Bananut-Electronics/MiDispositivoMIDI_V3/images/bananut.png

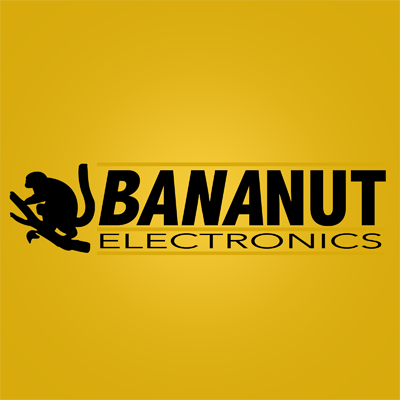
images/bananut.png
