Bananut-Electronics/MiDispositivoMIDI_V3/images/bot.png

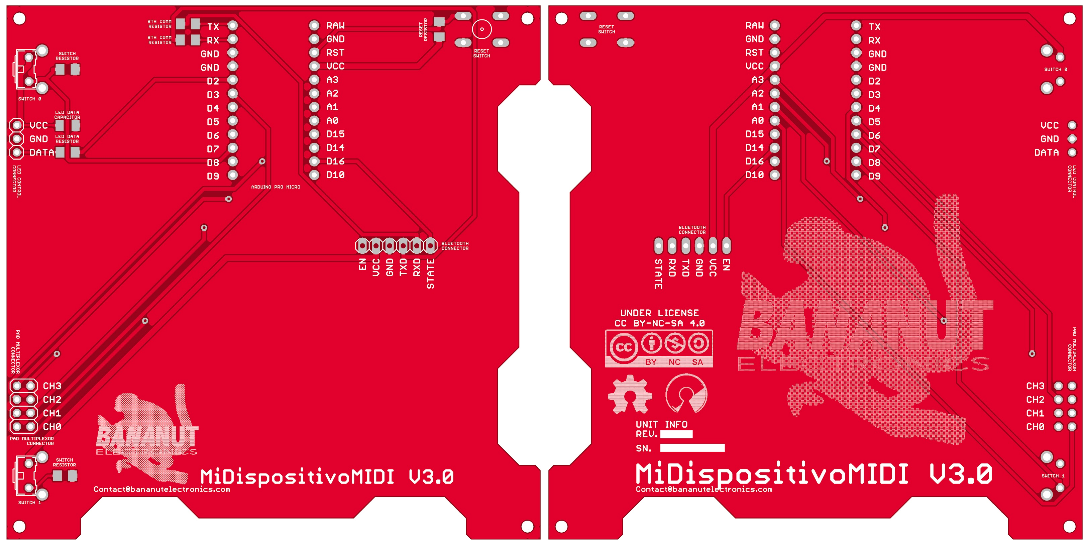
images/bot.png
