Bananut-Electronics/MiDispositivoMIDI_V3/images/front.jpg

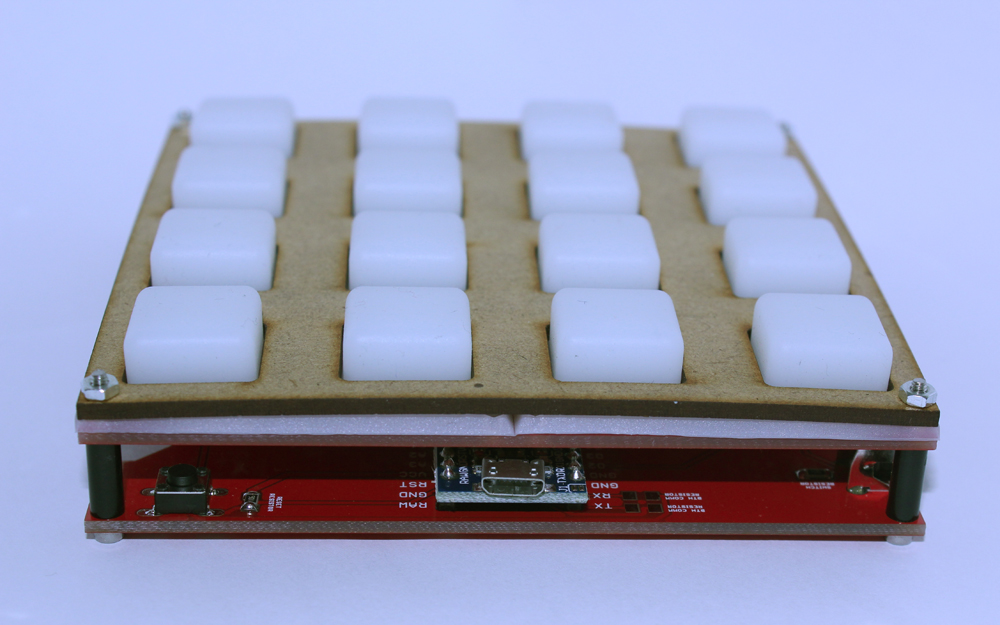
images/front.jpg
