Bananut-Electronics/MiDispositivoMIDI_V3/images/green.jpg

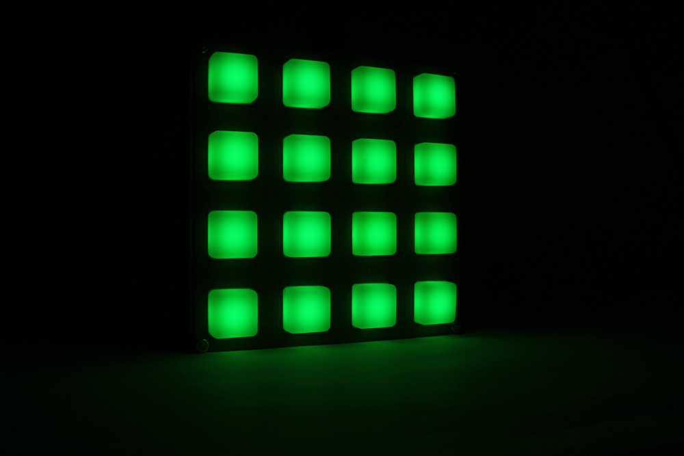
images/green.jpg
