Bananut-Electronics/MiDispositivoMIDI_V3/images/MDM_V3_HW_Arduino.jpg

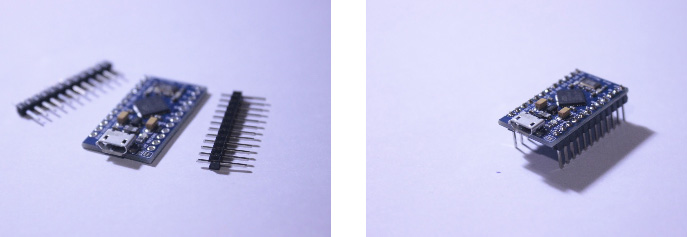
images/MDM_V3_HW_Arduino.jpg
