Bananut-Electronics/MiDispositivoMIDI_V3/images/MDM_V3_HW_ArduinoPinOut.jpg

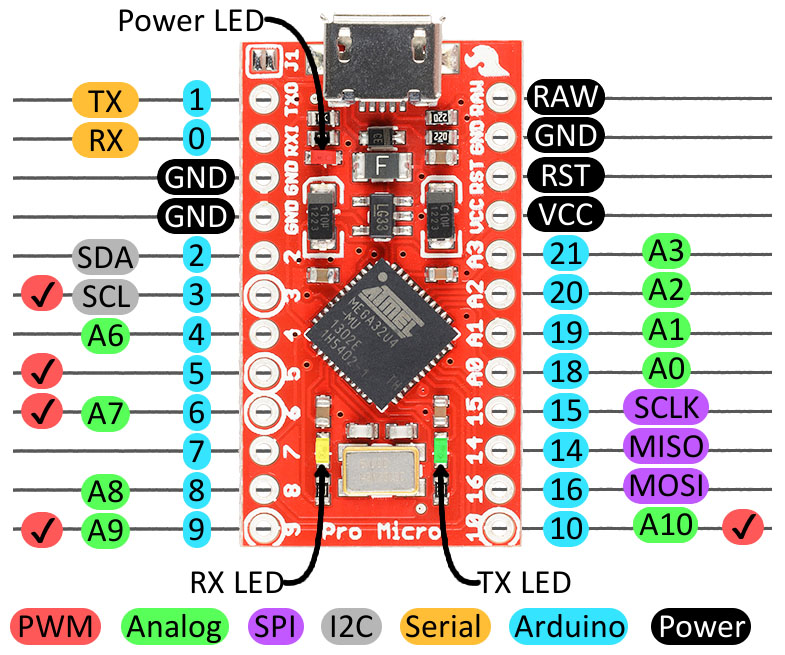
images/MDM_V3_HW_ArduinoPinOut.jpg
