Bananut-Electronics/MiDispositivoMIDI_V3/images/MDM_V3_HW_ControlBoard_PCBCon.JPG

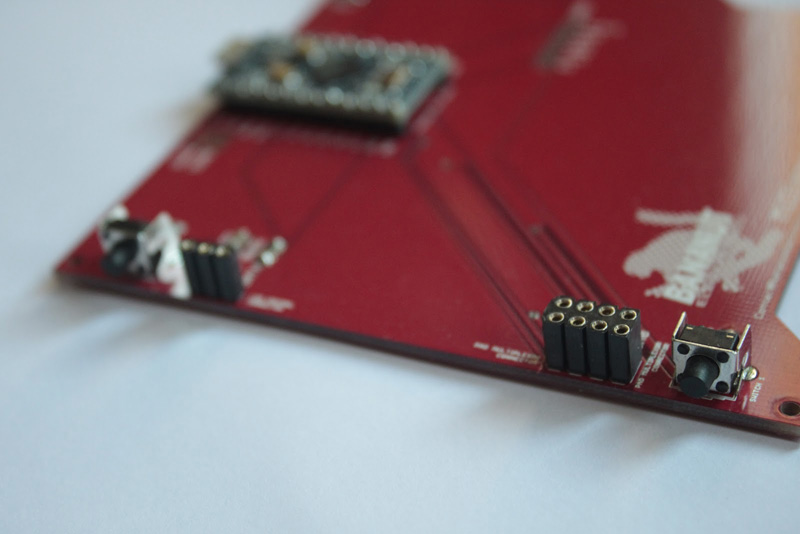
images/MDM_V3_HW_ControlBoard_PCBCon.JPG
