Bananut-Electronics/MiDispositivoMIDI_V3/images/MDM_V3_HW_LEDPad_Connector.JPG

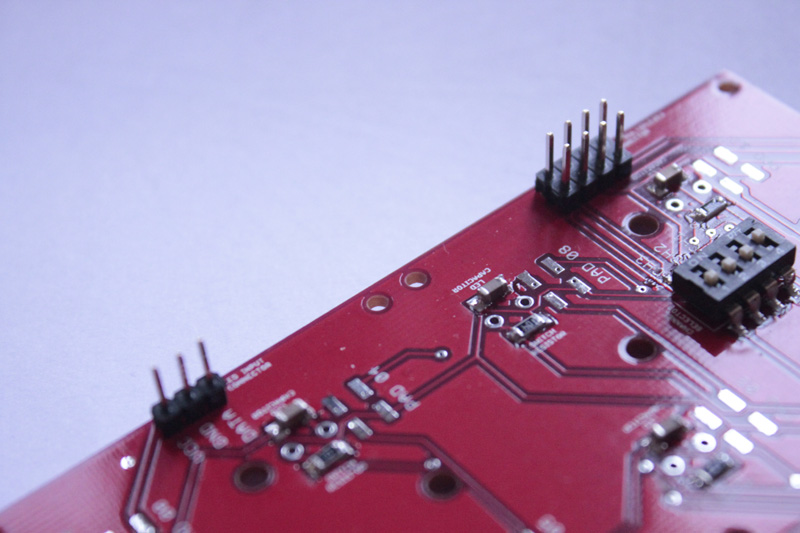
images/MDM_V3_HW_LEDPad_Connector.JPG
