Bananut-Electronics/MiDispositivoMIDI_V3/images/MDM_V3_HW_LEDPad_DIPSW.JPG

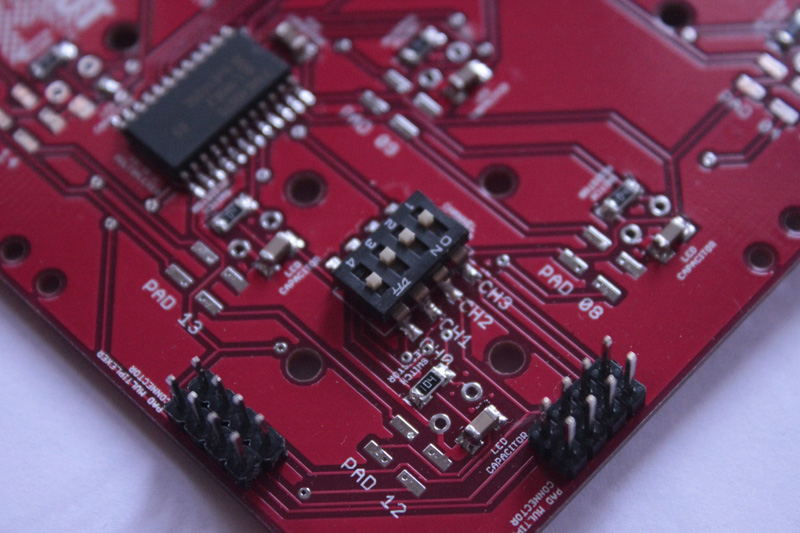
images/MDM_V3_HW_LEDPad_DIPSW.JPG
