Bananut-Electronics/MiDispositivoMIDI_V3/images/MDM_V3_HW_LEDPAD_Layer.jpg

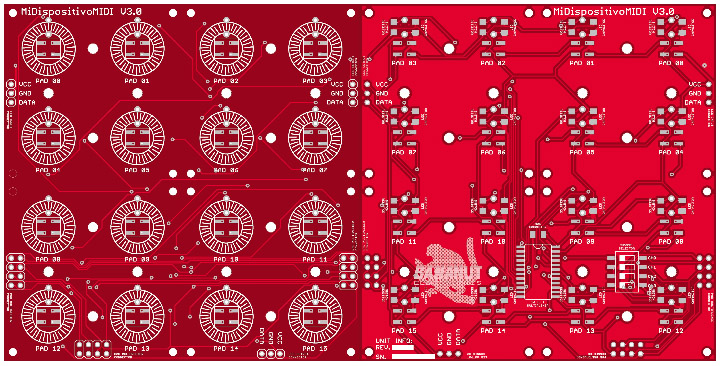
images/MDM_V3_HW_LEDPAD_Layer.jpg
