Bananut-Electronics/MiDispositivoMIDI_V3/images/MDM_V3_HW_LEDPad_SW.JPG

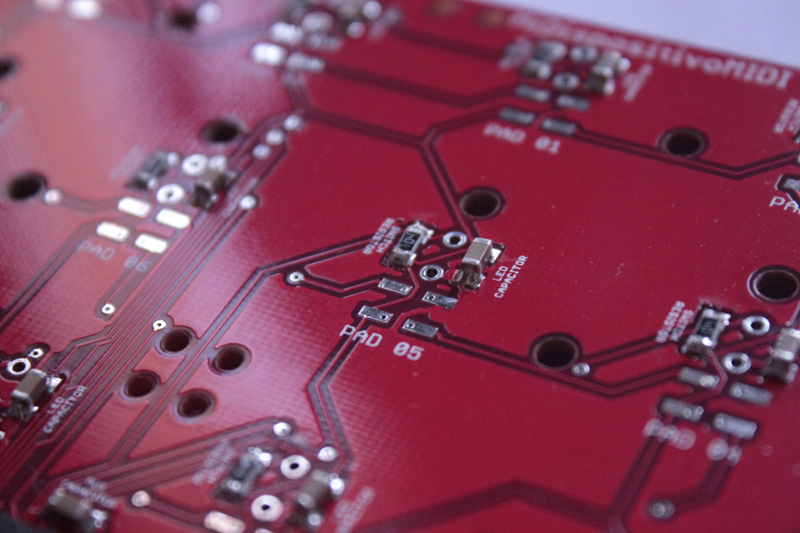
images/MDM_V3_HW_LEDPad_SW.JPG
