Bananut-Electronics/MiDispositivoMIDI_V3/images/MDM_V3_HW_MuxCode.jpg

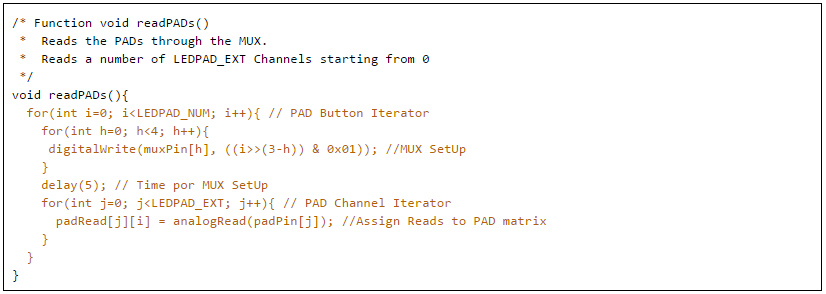
images/MDM_V3_HW_MuxCode.jpg
