Bananut-Electronics/MiDispositivoMIDI_V3/images/MDM_V3_HW_Render.jpg

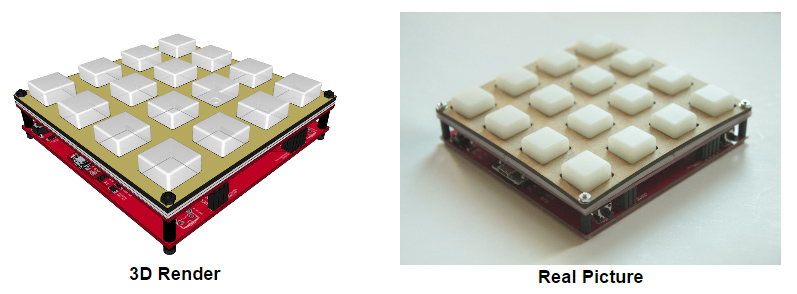
images/MDM_V3_HW_Render.jpg
