Bananut-Electronics/MiDispositivoMIDI_V3/images/MDM_V3_HW_ResetSwitch.JPG

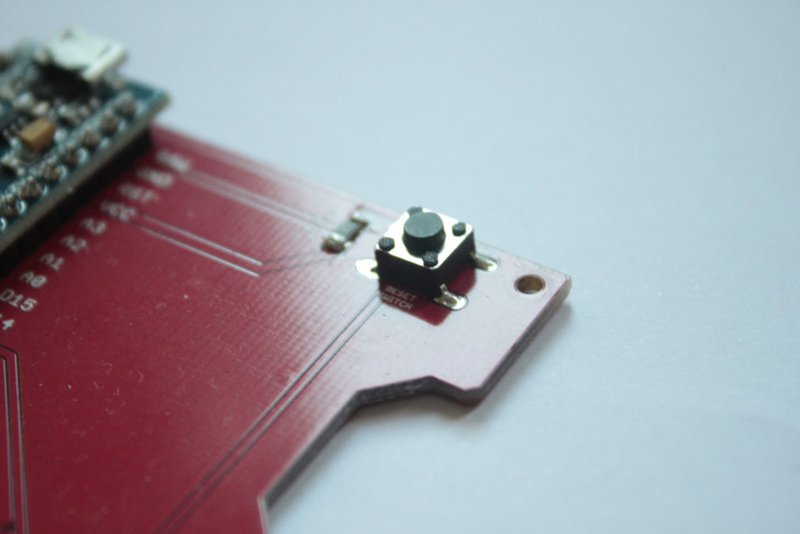
images/MDM_V3_HW_ResetSwitch.JPG
