Bananut-Electronics/MiDispositivoMIDI_V3/images/MDM_V3_HW_SWCircuit.jpg

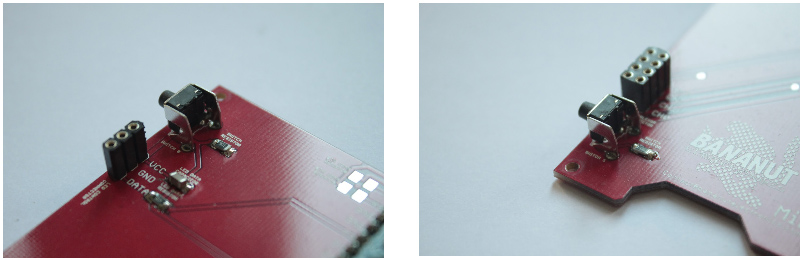
images/MDM_V3_HW_SWCircuit.jpg
