Bananut-Electronics/MiDispositivoMIDI_V3/images/MDM_V3_HW_WS2812B.jpg

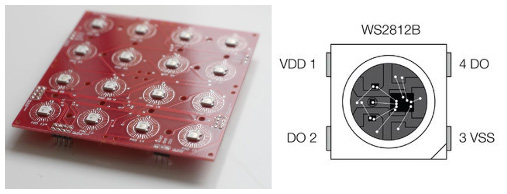
images/MDM_V3_HW_WS2812B.jpg
