Bananut-Electronics/MiDispositivoMIDI_V3/images/MDM_V3_INTRO_Device1.JPG

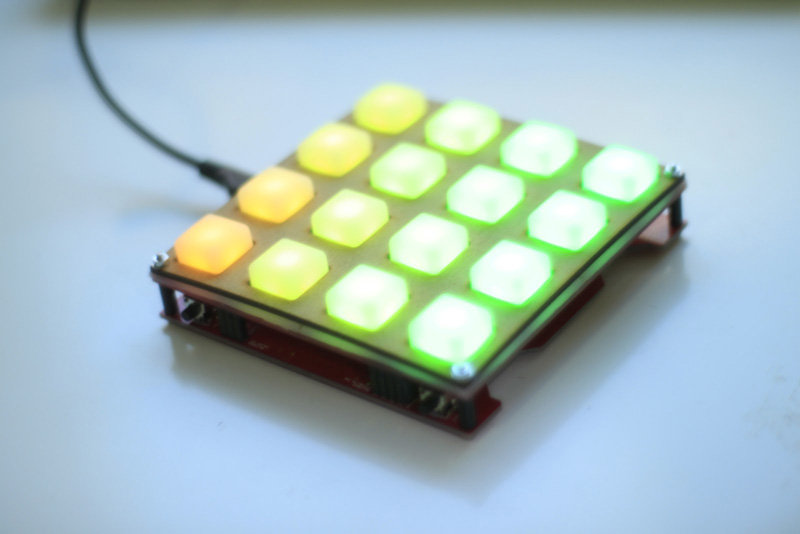
images/MDM_V3_INTRO_Device1.JPG
