Bananut-Electronics/MiDispositivoMIDI_V3/images/top.jpg

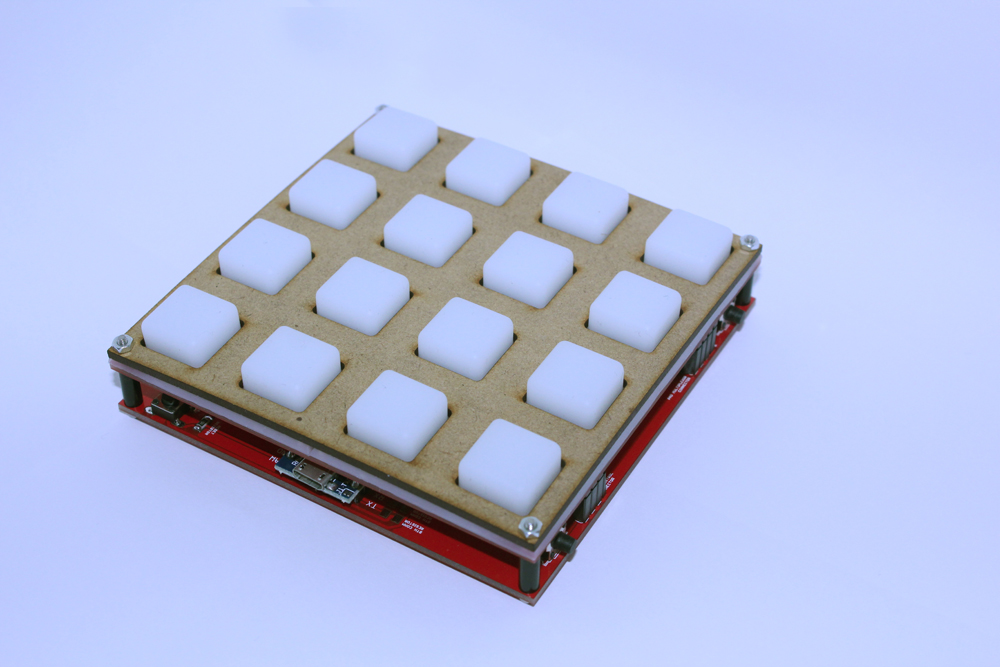
images/top.jpg
