Bananut-Electronics/MiDispositivoMIDI_V3/images/top.png

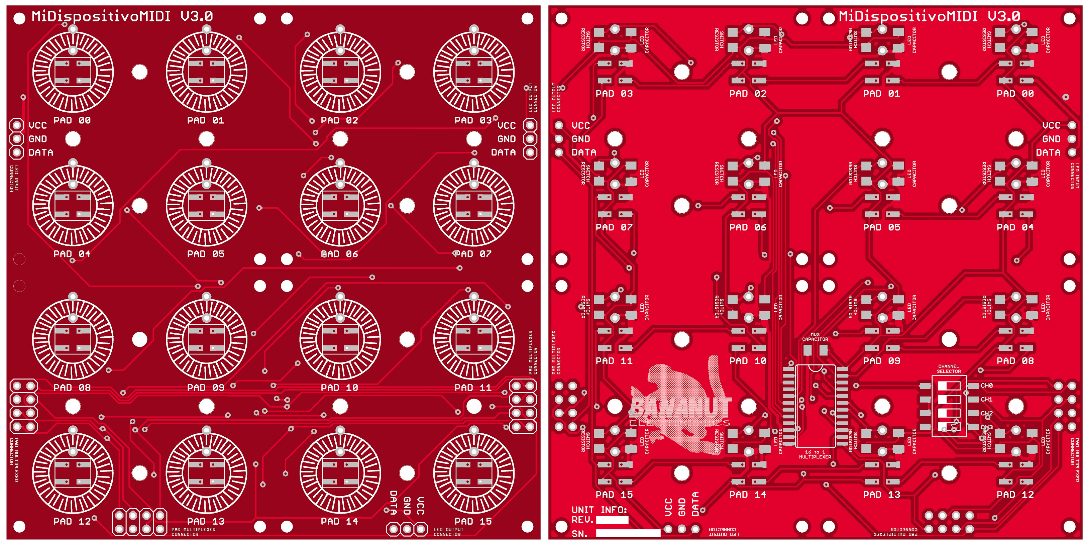
images/top.png
