Bananut-Electronics/MiDispositivoMIDI_V3/images/yellow.jpg

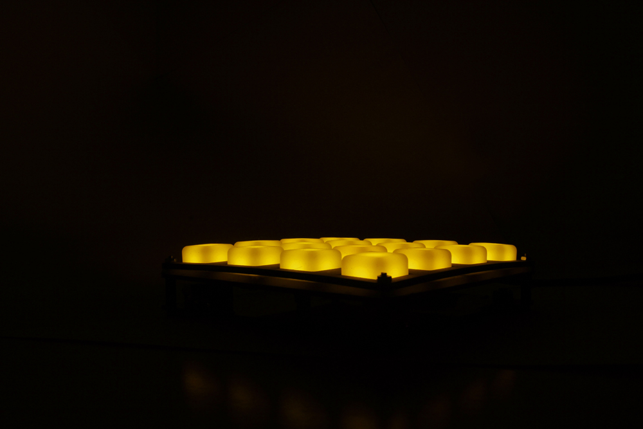
images/yellow.jpg
