Bananut-Electronics/MiDispositivoMIDI_V3/images/MDM_V3_HW_ArduinoSoldered.jpg

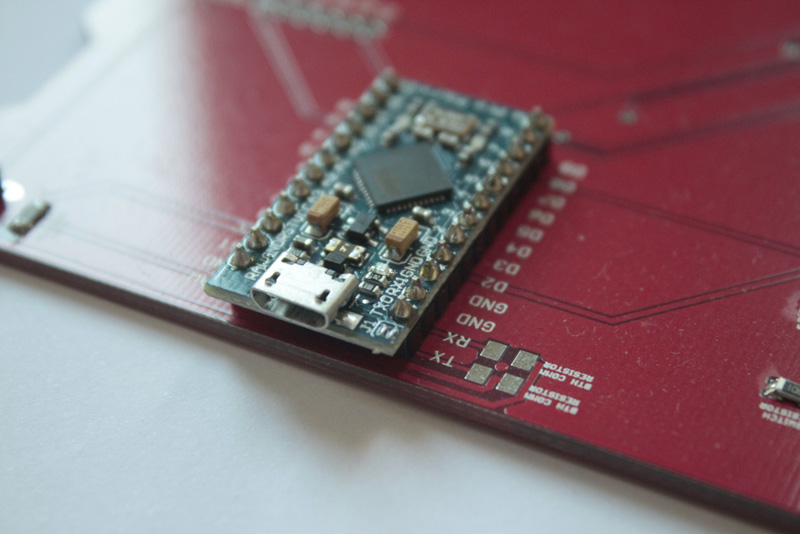
images/MDM_V3_HW_ArduinoSoldered.jpg
