Bananut-Electronics/MiDispositivoMIDI_V3/images/MDM_V3_HW_Assembled.JPG

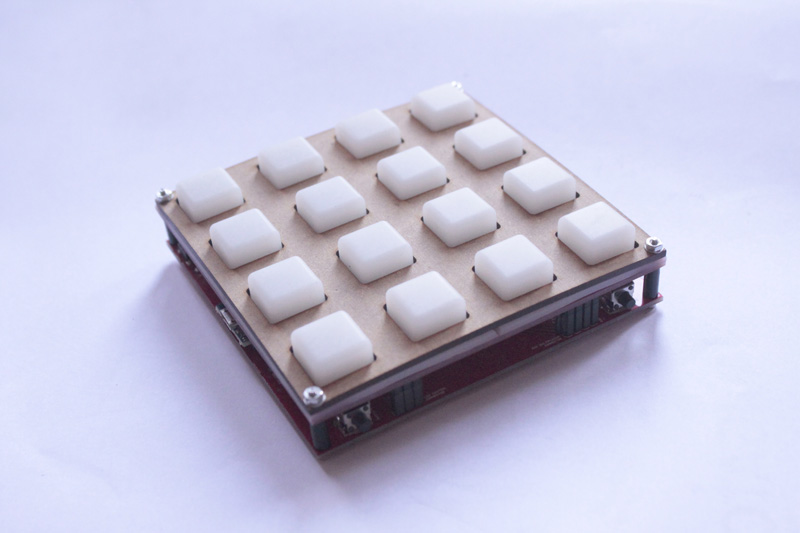
images/MDM_V3_HW_Assembled.JPG
