Bananut-Electronics/MiDispositivoMIDI_V3/images/MDM_V3_HW_ControlBoardSoldered.jpg

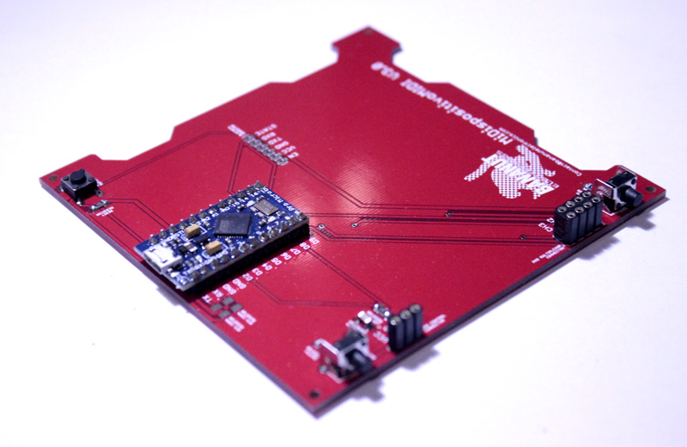
images/MDM_V3_HW_ControlBoardSoldered.jpg
